frankyhub/Cloudya/3D/box/box.png

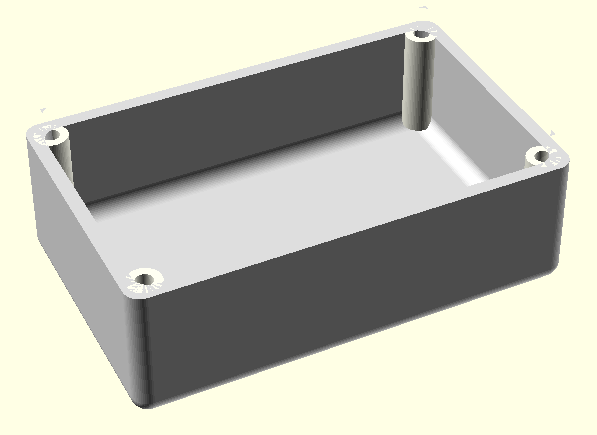
3D/box/box.png
