frankyhub/Cloudya/lbrn/BOXES_PY.png

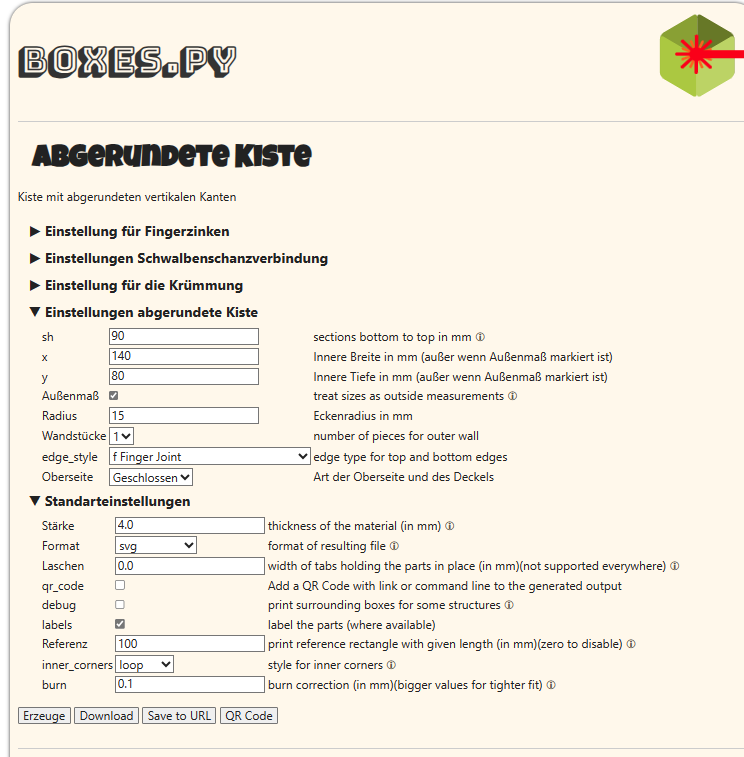
lbrn/BOXES_PY.png
