frankyhub/Cloudya/pic/basebox.png

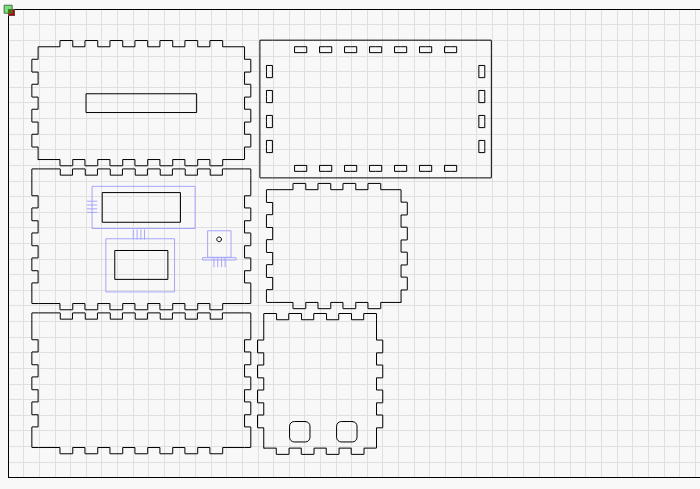
pic/basebox.png
