frankyhub/Cloudya/pic/cloudya.png

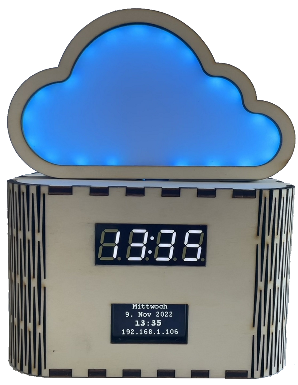
pic/cloudya.png
