frankyhub/Cloudya/pic/IMG_9629.jpg

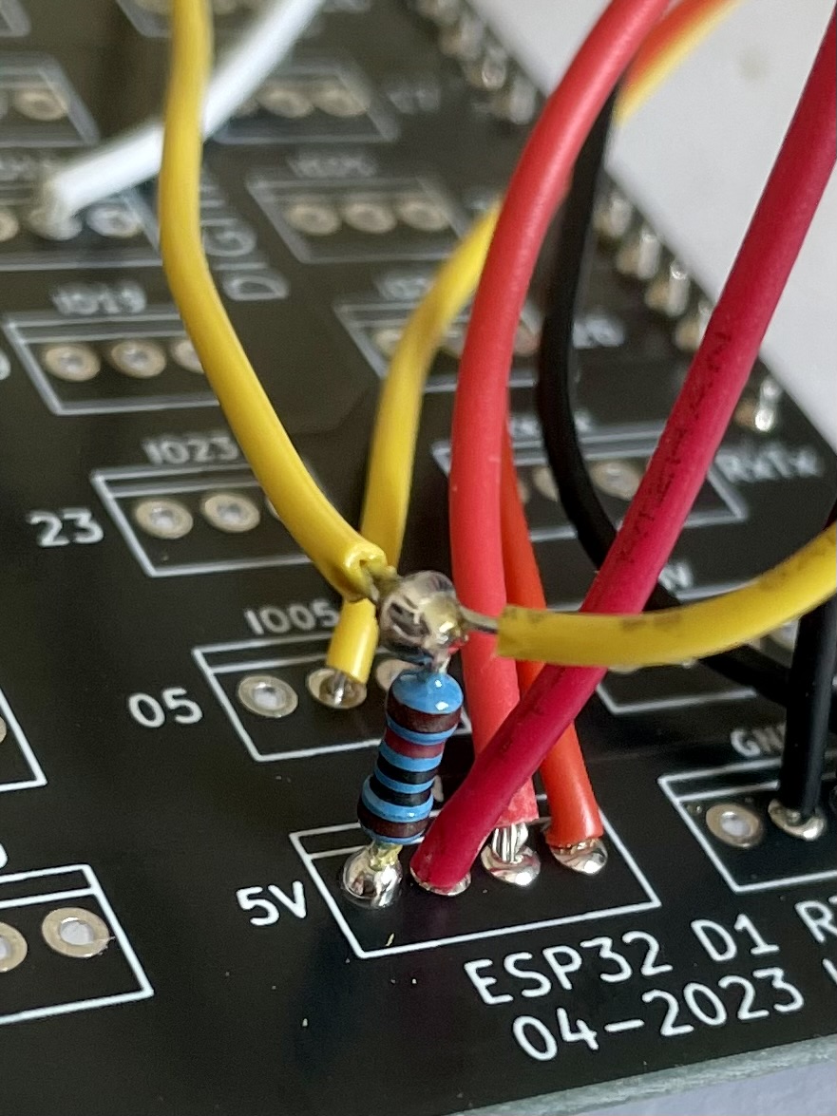
pic/IMG_9629.jpg
