frankyhub/Cloudya/pic/IMG_9630.jpg

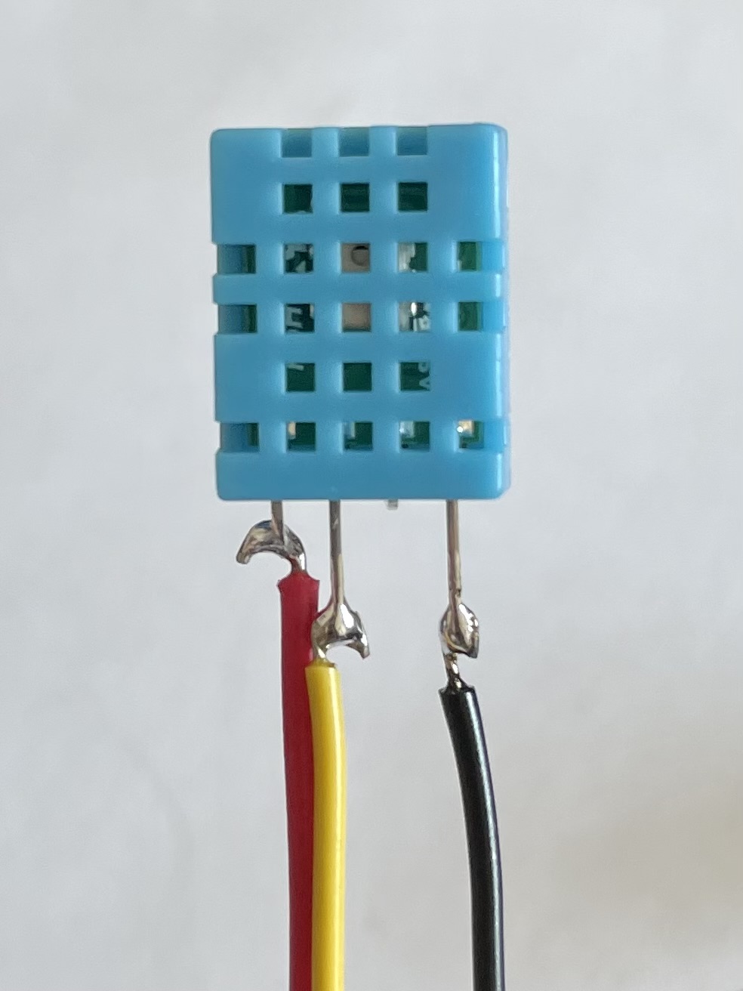
pic/IMG_9630.jpg
