frankyhub/Cloudya/pic/IMG_9631.jpg

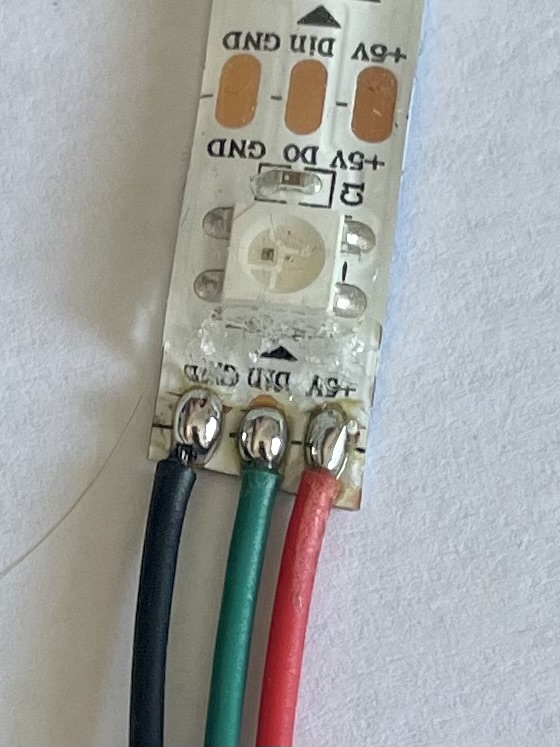
pic/IMG_9631.jpg
