frankyhub/Cloudya/3D/DHT11-Halter.scad

//DHT11-Halterung

difference() {
cube(size = [18,8,20.5], center = true);

translate(v = [-6.5, -2, -8])
cube(size = [13,7,18.5]);
   
}

/*
translate(v = [-12, -4, 10])
cube(size = [24,4,1.5]);

translate(v = [-10, -2, -8])
color( "red", 1.0 )
cube(size = [12.5,5.8,18]);
*/
