frankyhub/Cloudya/3D/OLED-Spacer1.scad

//OLED 1.3 Diplay Spacer für Cloudya


difference(){
cube([2,44,34]); //innen

translate([-0.1,4,6])
cube([3,36,24]); //innen
    
translate([-0.1,13,4])
cube([3,17,50]); //innen      
}
