frankyhub/Cloudya/3D/TM-Spacer.scad

cube([4,40,4]);
